Aaron-Ace/DLAOIBOT/output/capture.png

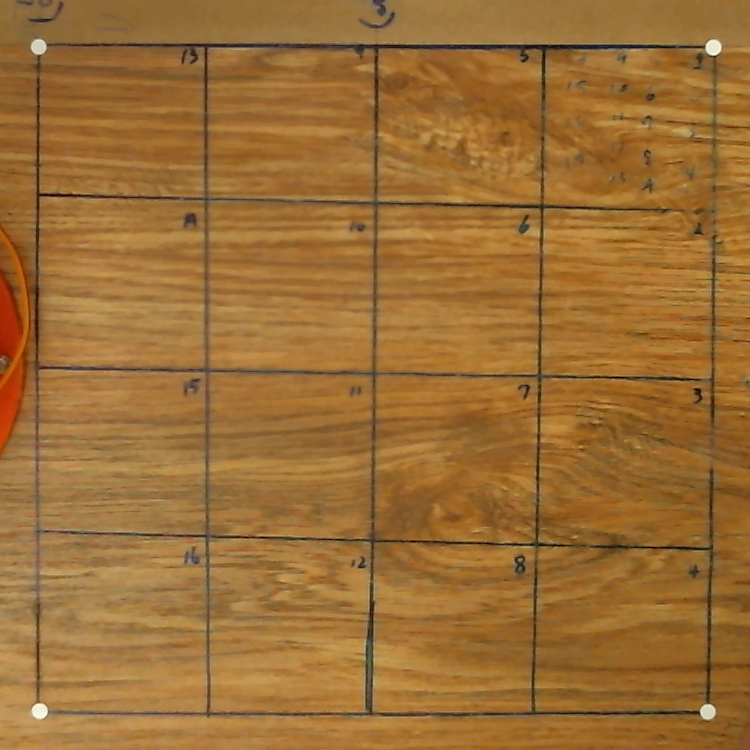
output/capture.png
