Aaron-Ace/DLAOIBOT/resource/yolo_3.png

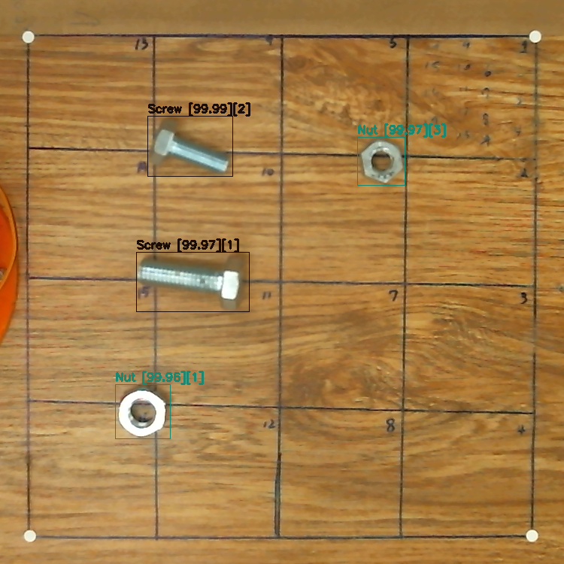
resource/yolo_3.png
