Aaron-Ace/DLAOIBOT/RoboticArm3DModel/Gripper 1.STL

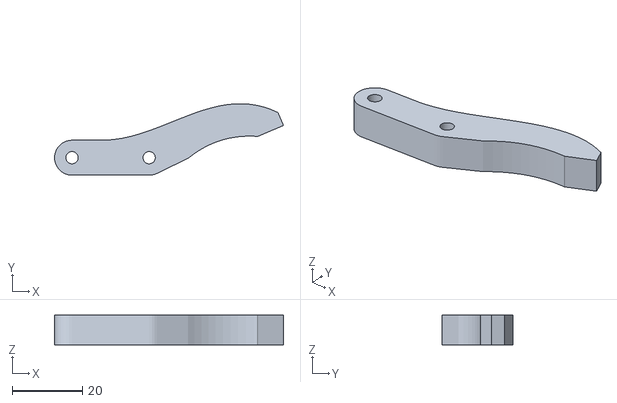
[picture p25: CAD file, 2021-05-14]
RoboticArm3DModel/Gripper 1.STL
65.3 x 20.4 x 8.50
