Aaron-Ace/DLAOIBOT/RoboticArm3DModel/Arduino Robot Arm 3D Model/Servo Motor Micro  9g.SLDPRT

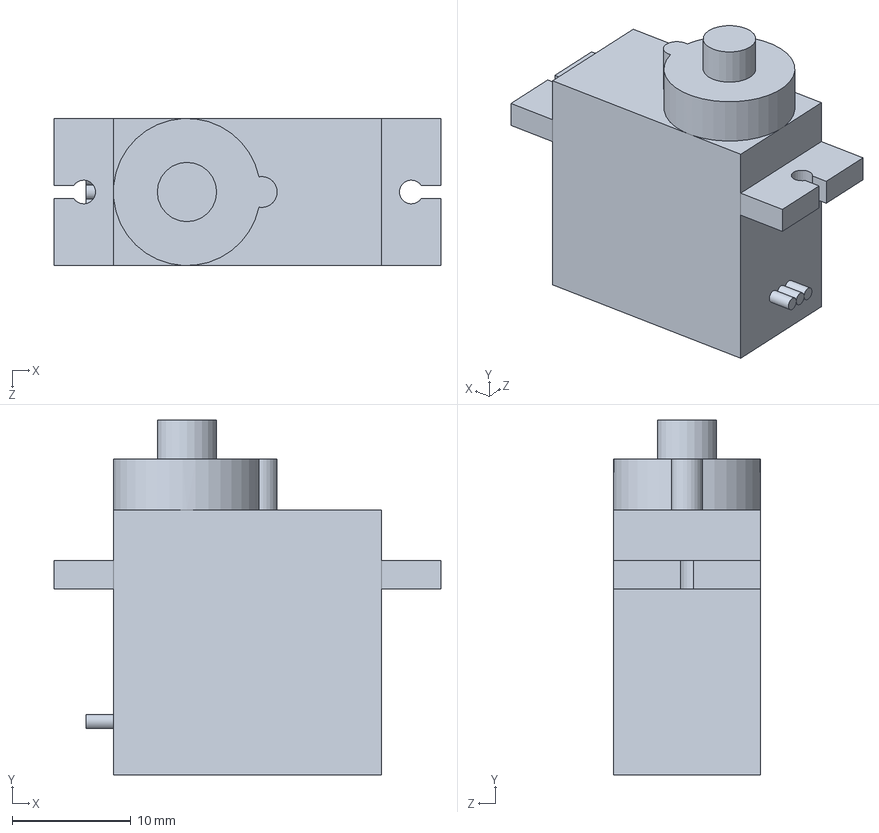
[picture p26: CAD file, 2021-05-14]
RoboticArm3DModel/Arduino Robot Arm 3D Model/Servo Motor Micro 9g.SLDPRT
32.6 x 29.9 x 12.4 mm
