Aaron-Ace/DLAOIBOT/RoboticArm3DModel/NATHANarm1.STL

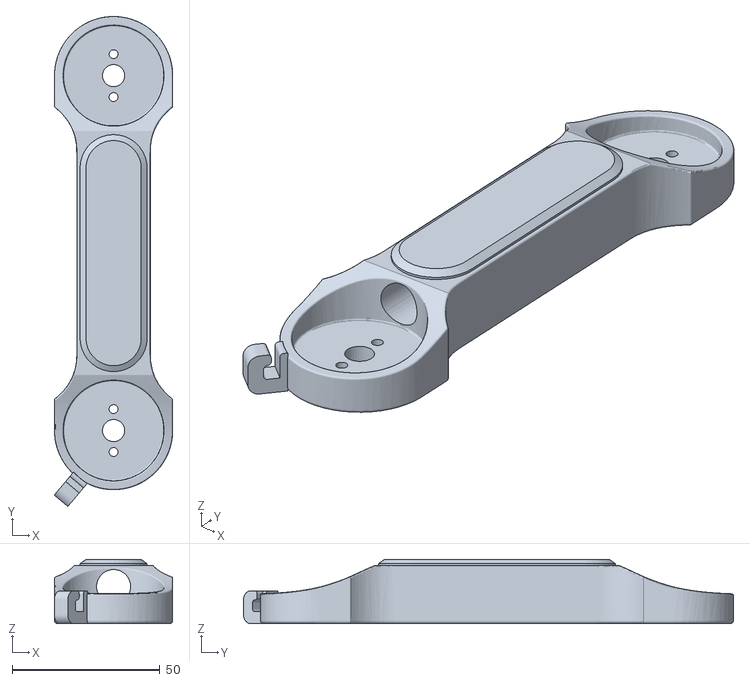
[picture p27: CAD file, 2021-05-14]
RoboticArm3DModel/NATHANarm1.STL
40.1 x 165.7 x 21.6
