Aaron-Ace/DLAOIBOT/RoboticArm3DModel/Arduino Robot Arm 3D Model/Base_r1.SLDPRT

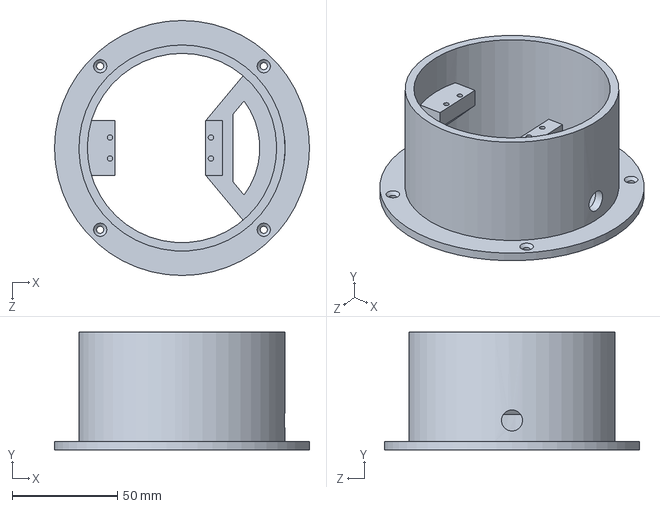
[picture p28: CAD file, 2021-05-14]
RoboticArm3DModel/Arduino Robot Arm 3D Model/Base_r1.SLDPRT
121.2 x 56.0 x 121.2 mm
