Aaron-Ace/DLAOIBOT/RoboticArm3DModel/Servo Motor MG996R.STL

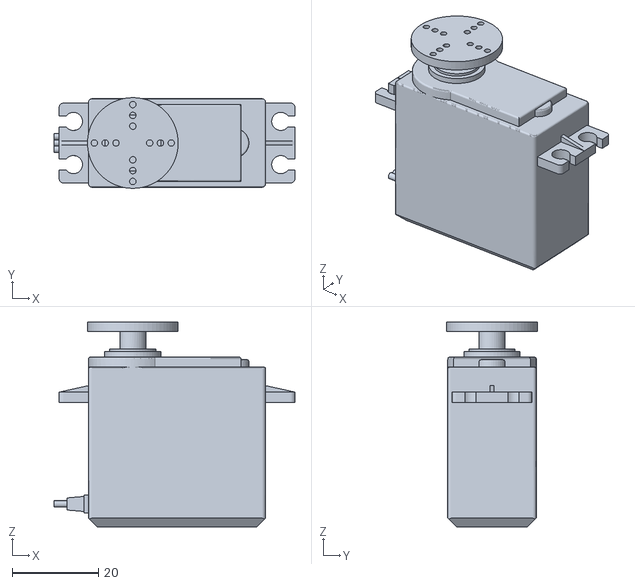
[picture p29: CAD file, 2021-05-14]
RoboticArm3DModel/Servo Motor MG996R.STL
55.8 x 21.0 x 47.4
