Aaron-Ace/DLAOIBOT/RoboticArm3DModel/Arduino Robot Arm 3D Model/Arm 02 v3.SLDPRT

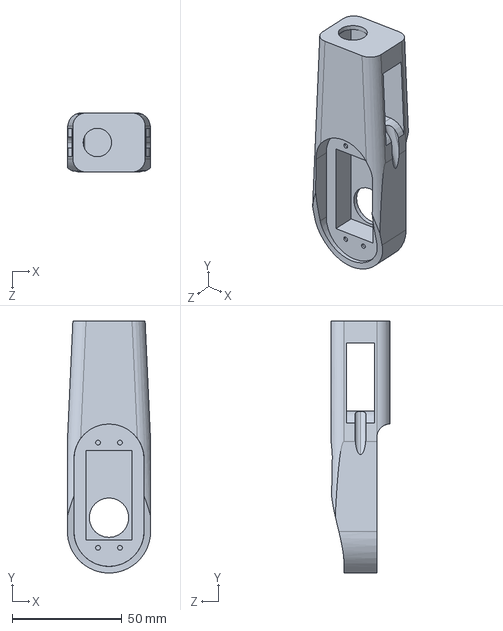
[picture p30: CAD file, 2021-05-14]
RoboticArm3DModel/Arduino Robot Arm 3D Model/Arm 02 v3.SLDPRT
38.0 x 115.0 x 27.0 mm
