Aaron-Ace/DLAOIBOT/RoboticArm3DModel/Arduino Robot Arm 3D Model/Gripper/Gripper 1_r1.SLDPRT

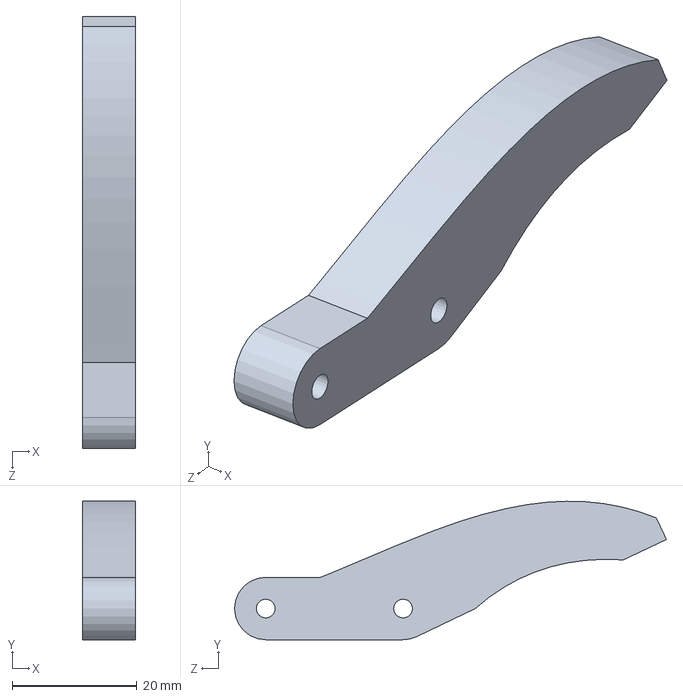
[picture p31: CAD file, 2021-05-14]
RoboticArm3DModel/Arduino Robot Arm 3D Model/Gripper/Gripper 1_r1.SLDPRT
8.50 x 22.2 x 69.2 mm
