Aaron-Ace/DLAOIBOT/RoboticArm3DModel/grip link 1.STL

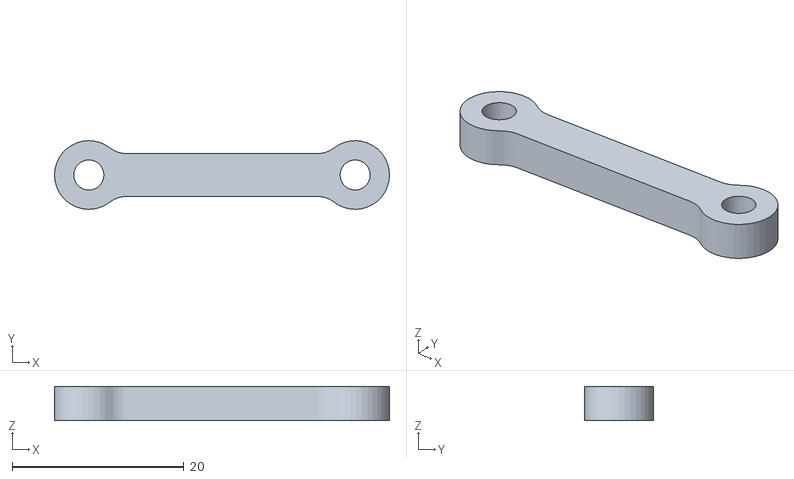
[picture p32: CAD file, 2021-05-14]
RoboticArm3DModel/grip link 1.STL
39.0 x 8.00 x 4.00
