Aaron-Ace/DLAOIBOT/RoboticArm3DModel/Arduino Robot Arm 3D Model/Gripper/grip link 1.SLDPRT

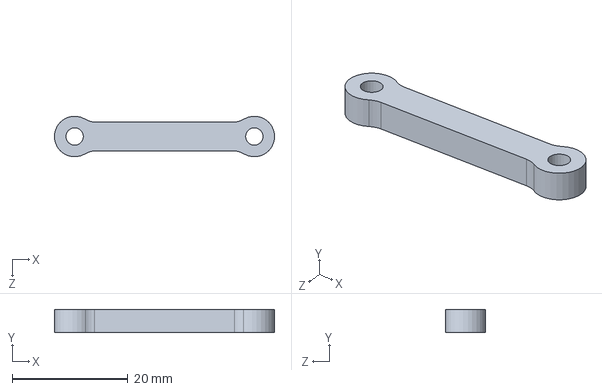
[picture p33: CAD file, 2021-05-14]
RoboticArm3DModel/Arduino Robot Arm 3D Model/Gripper/grip link 1.SLDPRT
38.0 x 4.00 x 6.96 mm
