Aaron-Ace/DLAOIBOT/RoboticArm3DModel/NATHANwaist.STL

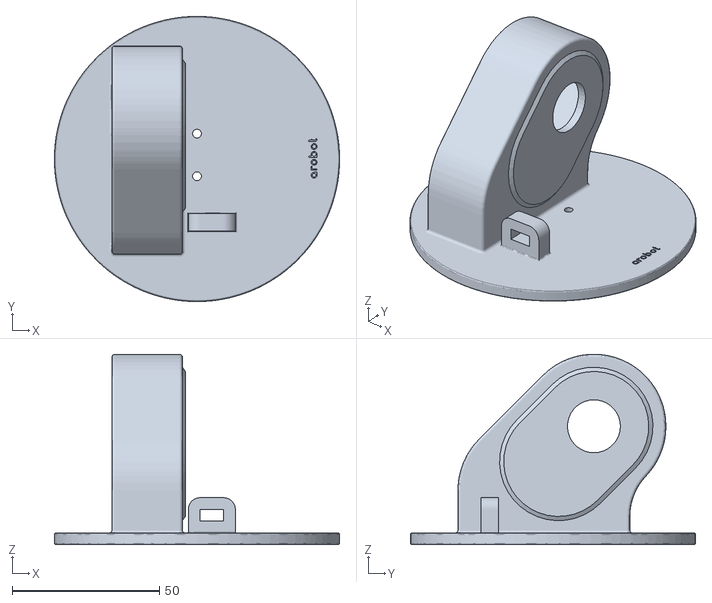
[picture p34: CAD file, 2021-05-14]
RoboticArm3DModel/NATHANwaist.STL
96.9 x 97.0 x 64.8
