Aaron-Ace/DLAOIBOT/RoboticArm3DModel/Arduino Robot Arm 3D Model/Test 01.SLDPRT

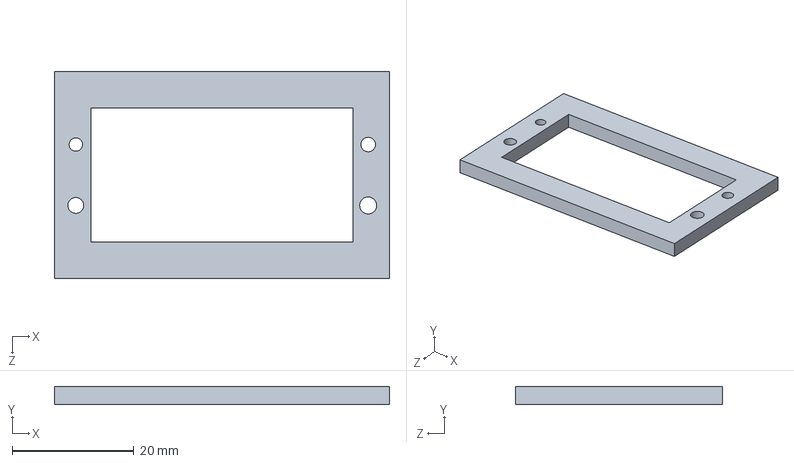
[picture p35: CAD file, 2021-05-14]
RoboticArm3DModel/Arduino Robot Arm 3D Model/Test 01.SLDPRT
55.0 x 3.00 x 34.0 mm
