Aaron-Ace/DLAOIBOT/RoboticArm3DModel/Arduino Robot Arm 3D Model/Arm 02.SLDPRT

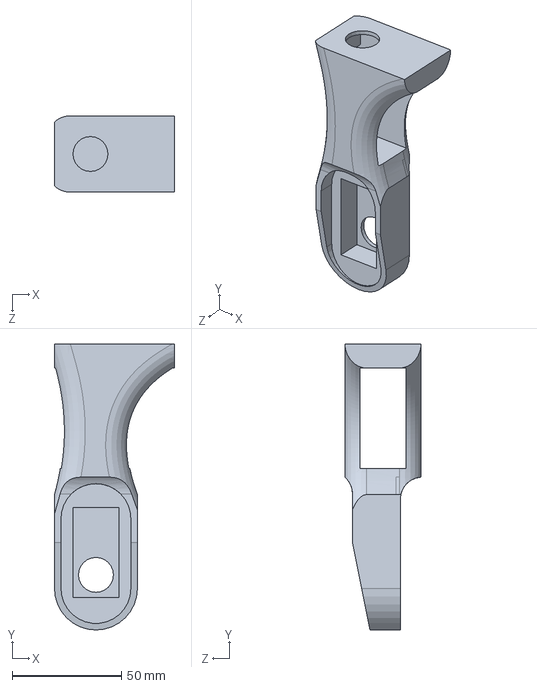
[picture p36: CAD file, 2021-05-14]
RoboticArm3DModel/Arduino Robot Arm 3D Model/Arm 02.SLDPRT
55.0 x 131.0 x 35.0 mm
